synaptics-cpt/tourmalet/Docs/Pictures/Full_size/5223_battery_contact.jpg

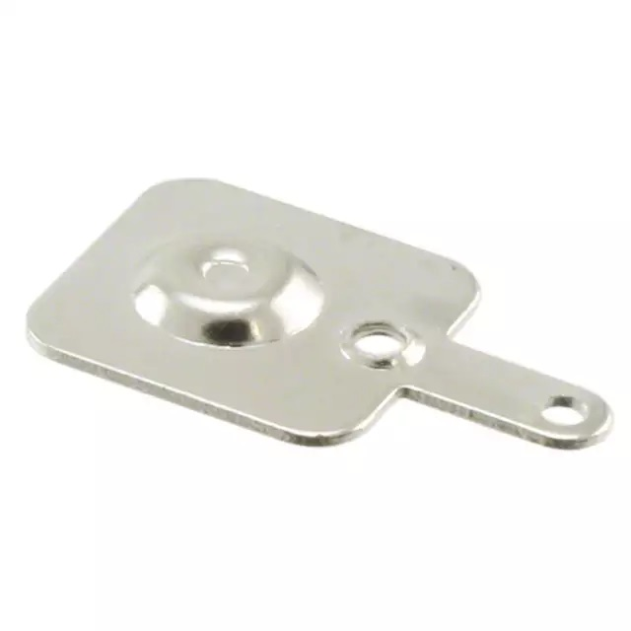
Docs/Pictures/Full_size/5223_battery_contact.jpg
