synaptics-cpt/tourmalet/Docs/Pictures/Full_size/attached_halves.jpg

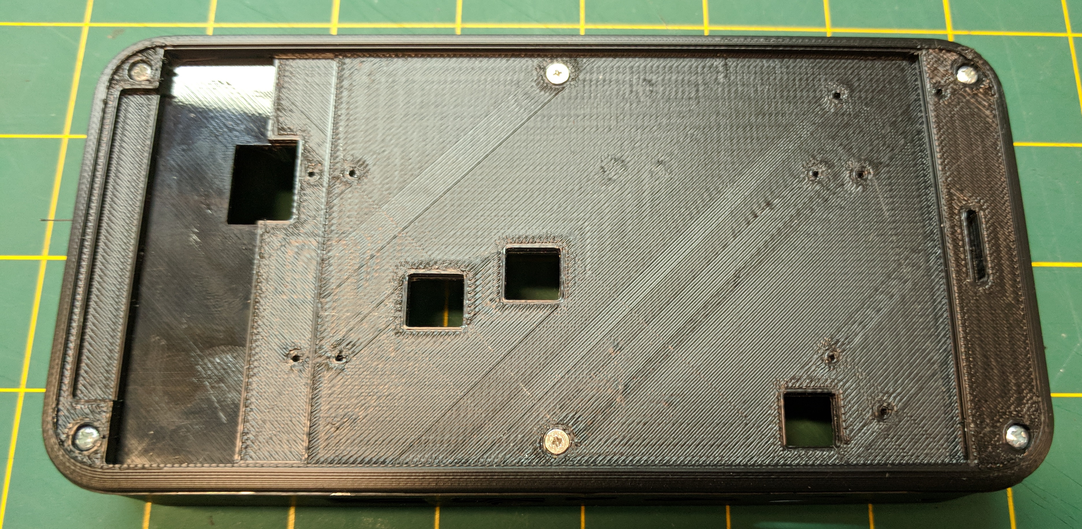
Docs/Pictures/Full_size/attached_halves.jpg
