synaptics-cpt/tourmalet/Docs/Pictures/Full_size/Back_no_battery.jpg

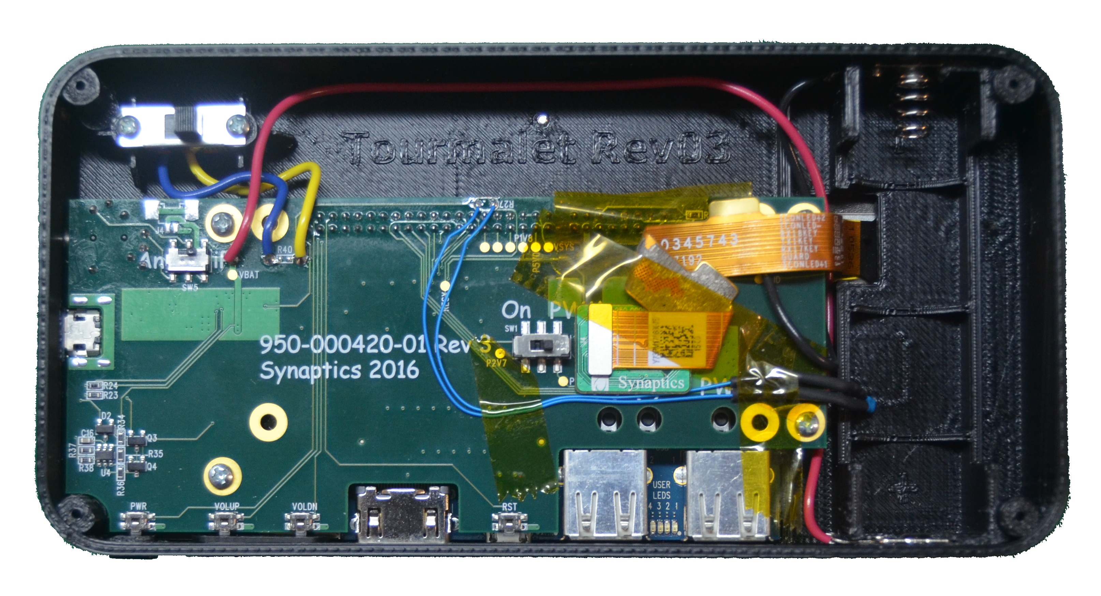
Docs/Pictures/Full_size/Back_no_battery.jpg
