synaptics-cpt/tourmalet/Docs/Pictures/Full_size/buttons.jpg

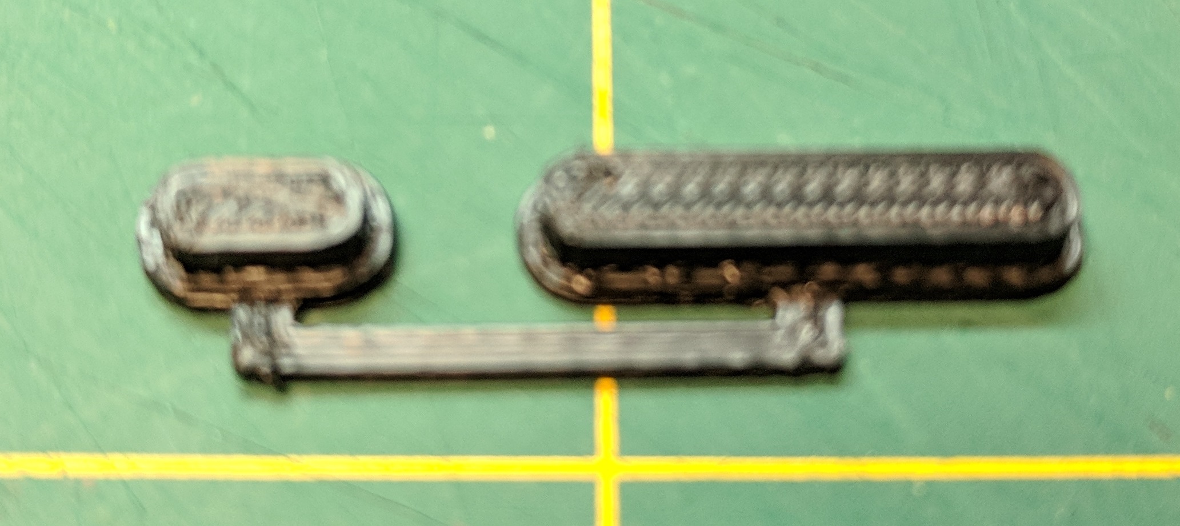
Docs/Pictures/Full_size/buttons.jpg
