synaptics-cpt/tourmalet/Docs/Pictures/Full_size/buttons_in.jpg

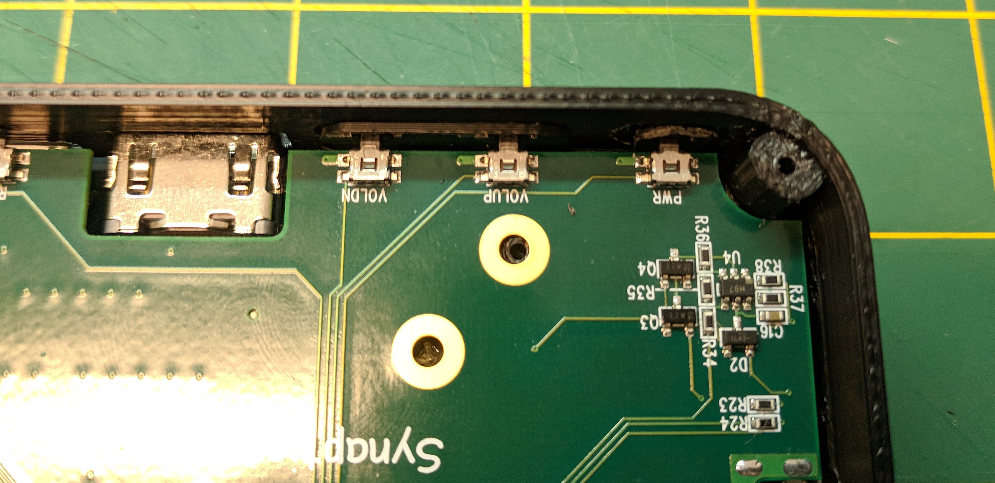
Docs/Pictures/Full_size/buttons_in.jpg
