synaptics-cpt/tourmalet/Docs/Pictures/Full_size/case_bottom.jpg

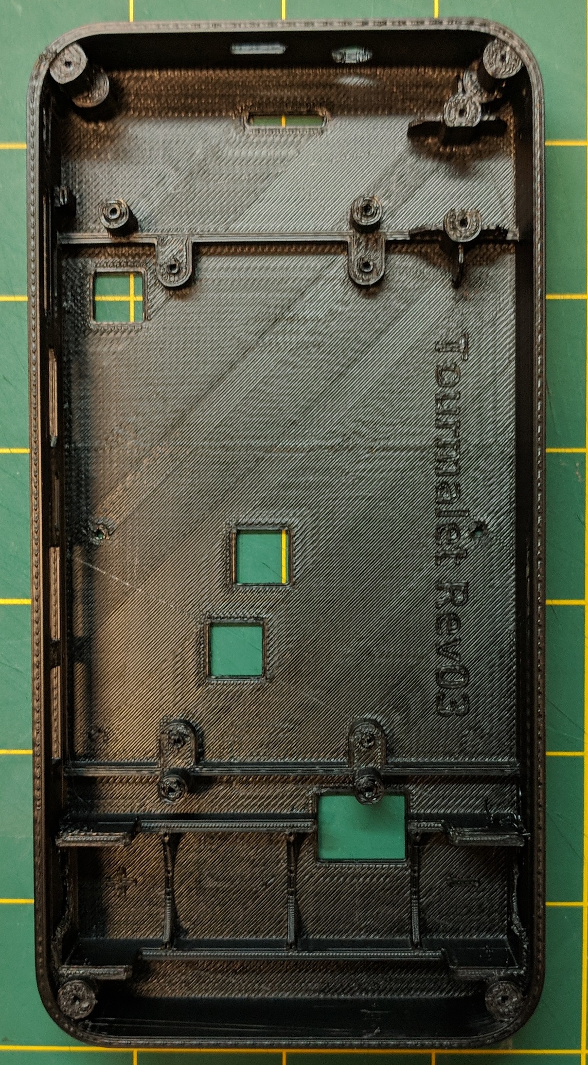
Docs/Pictures/Full_size/case_bottom.jpg
