synaptics-cpt/tourmalet/Docs/Pictures/Full_size/case_halves.jpg

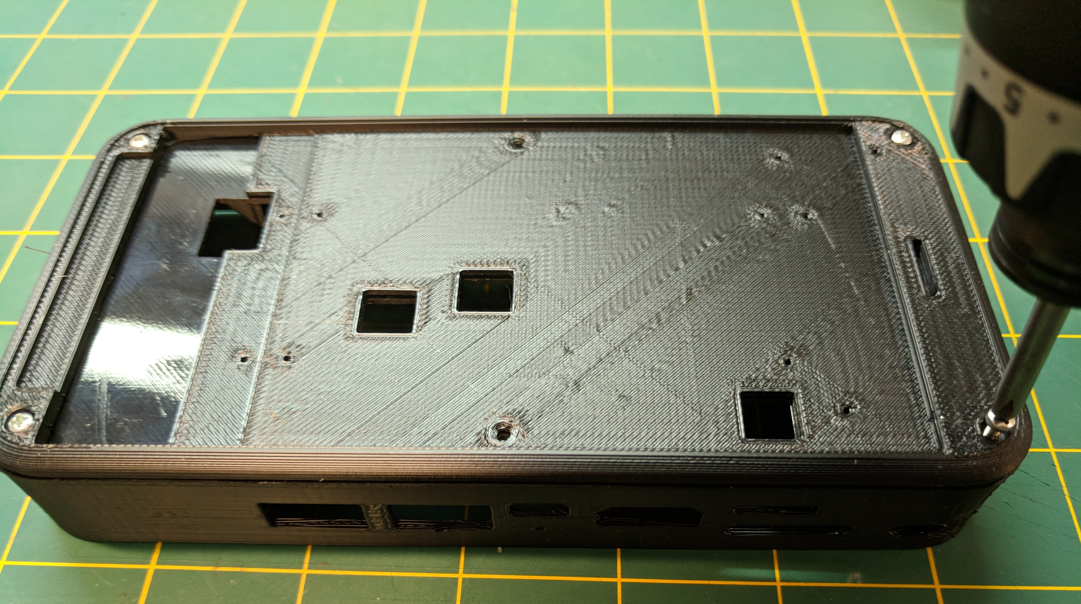
Docs/Pictures/Full_size/case_halves.jpg
