synaptics-cpt/tourmalet/Docs/Pictures/Full_size/case_top.jpg

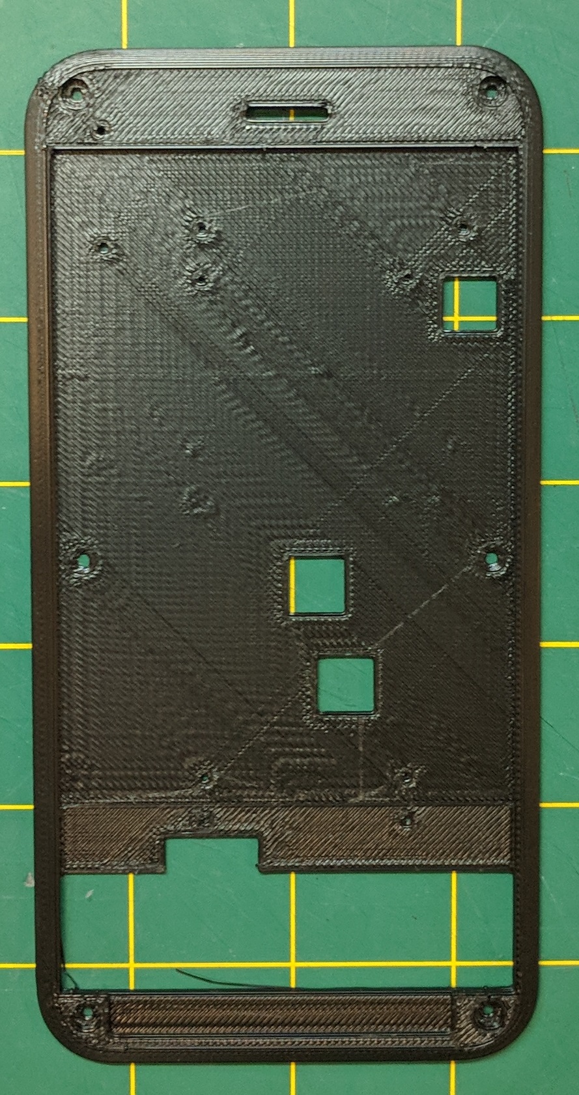
Docs/Pictures/Full_size/case_top.jpg
