synaptics-cpt/tourmalet/Docs/Pictures/Full_size/daughter_board_in.jpg

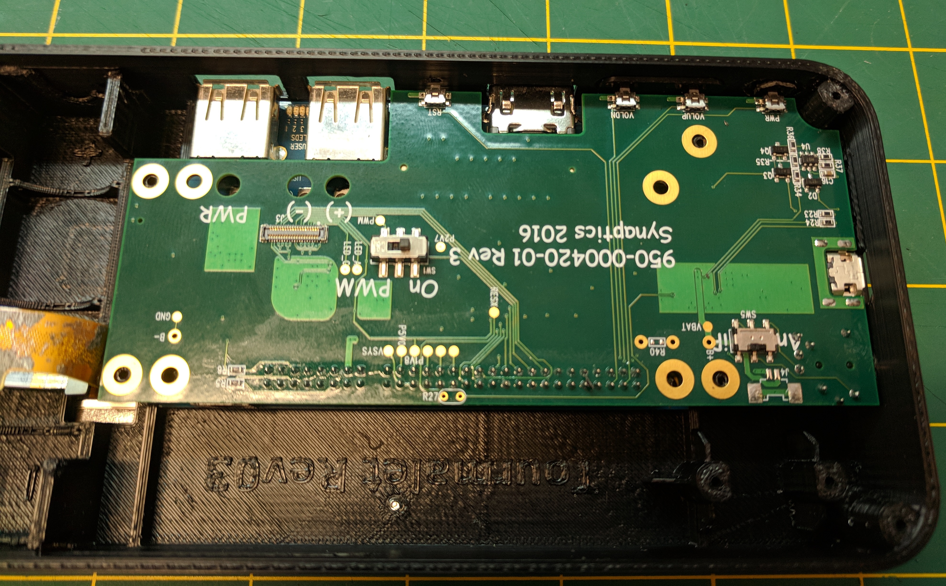
Docs/Pictures/Full_size/daughter_board_in.jpg
