synaptics-cpt/tourmalet/Docs/Pictures/Full_size/dragonboard_in_housing.jpg

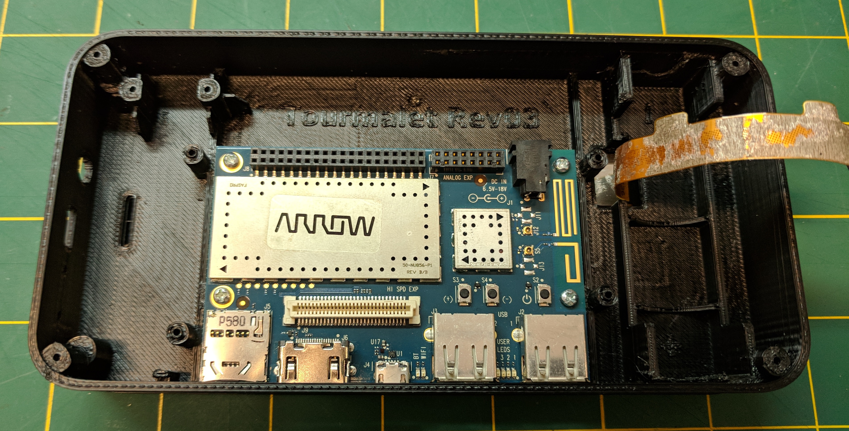
Docs/Pictures/Full_size/dragonboard_in_housing.jpg
