synaptics-cpt/tourmalet/Docs/Pictures/Full_size/fastboot_enable.jpg

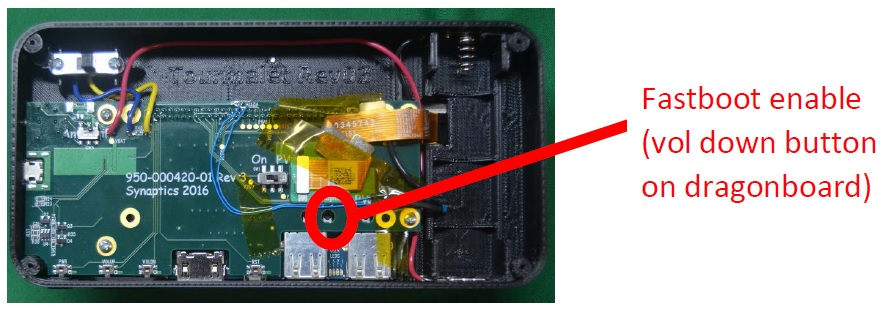
Docs/Pictures/Full_size/fastboot_enable.jpg
