synaptics-cpt/tourmalet/Docs/Pictures/Full_size/Glamor_shot_v1device.jpg

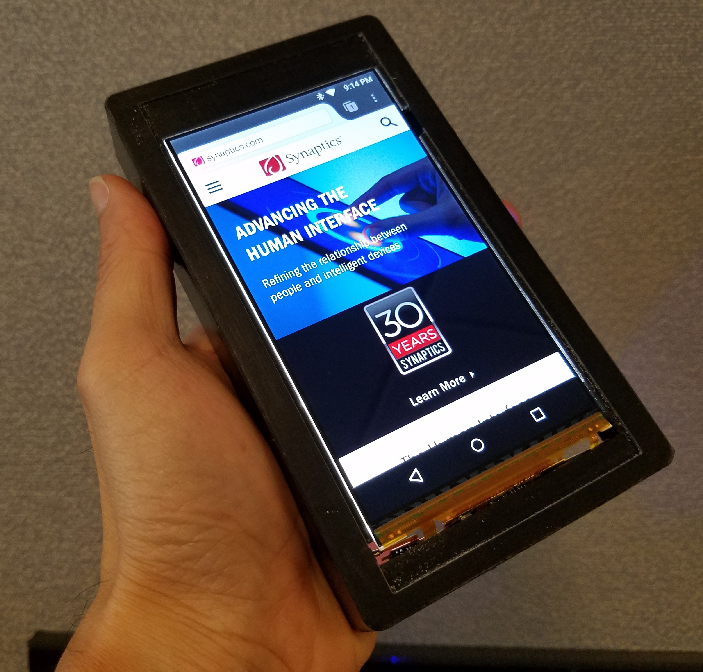
Docs/Pictures/Full_size/Glamor_shot_v1device.jpg
