synaptics-cpt/tourmalet/Docs/Pictures/Full_size/Headphone_switch.jpg

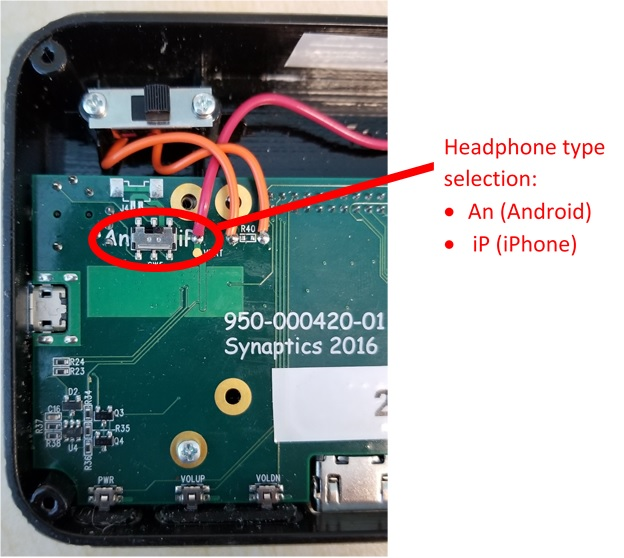
Docs/Pictures/Full_size/Headphone_switch.jpg
