synaptics-cpt/tourmalet/Docs/Pictures/Full_size/Home_screen.jpg

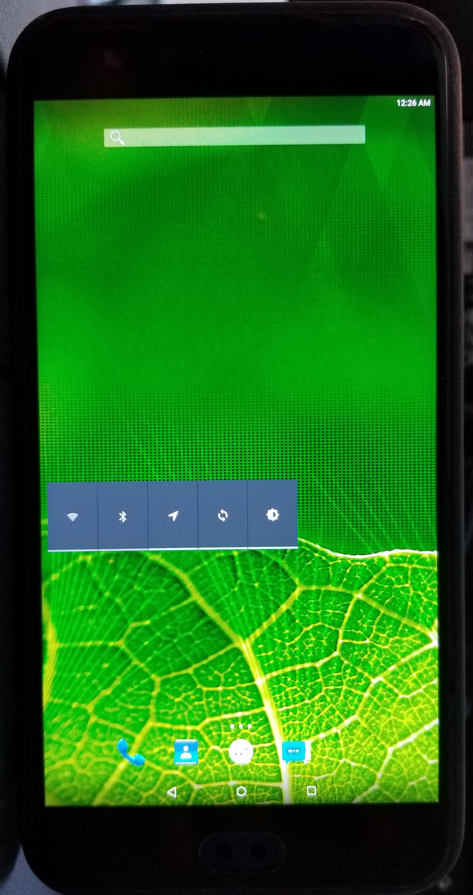
Docs/Pictures/Full_size/Home_screen.jpg
