synaptics-cpt/tourmalet/Docs/Pictures/Full_size/lcd_adapter.jpg

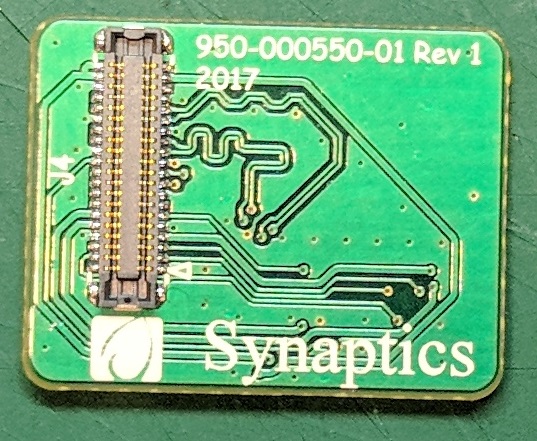
Docs/Pictures/Full_size/lcd_adapter.jpg
