synaptics-cpt/tourmalet/Docs/Pictures/Full_size/Lock_screen.jpg

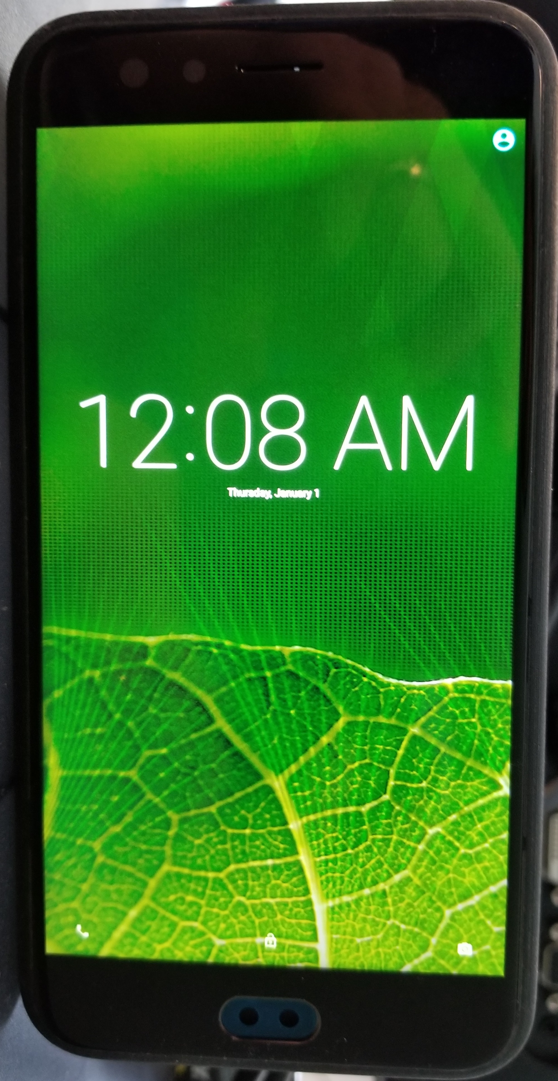
Docs/Pictures/Full_size/Lock_screen.jpg
