synaptics-cpt/tourmalet/Docs/Pictures/Full_size/negative_wire.jpg

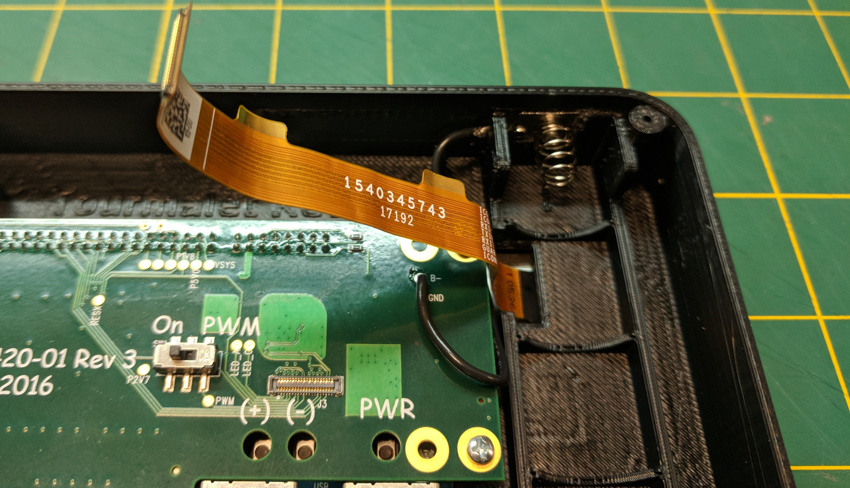
Docs/Pictures/Full_size/negative_wire.jpg
