synaptics-cpt/tourmalet/Docs/Pictures/Full_size/screen_adhesive_bottom.jpg

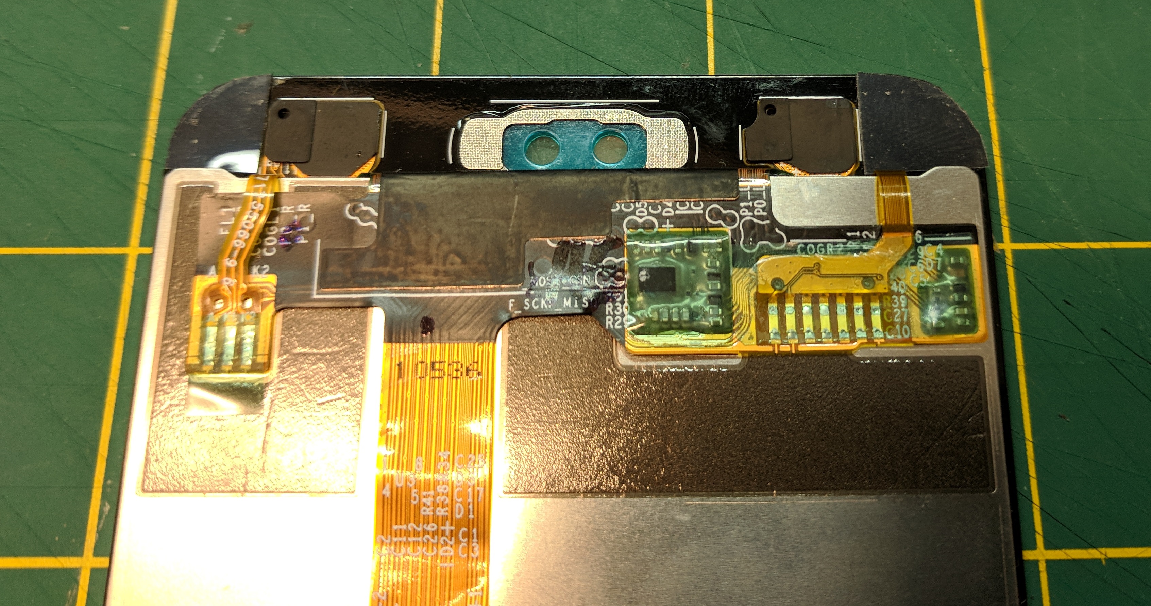
Docs/Pictures/Full_size/screen_adhesive_bottom.jpg
