synaptics-cpt/tourmalet/Docs/Pictures/Full_size/screen_adhesive_top.jpg

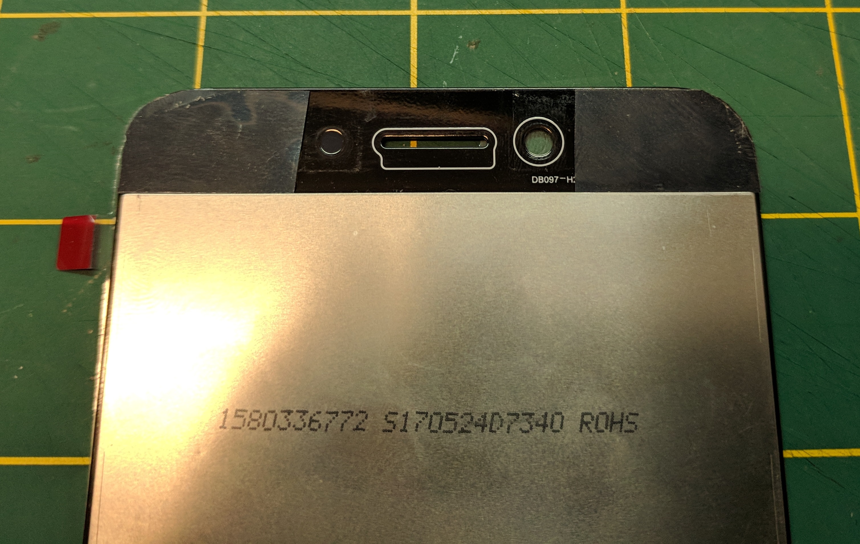
Docs/Pictures/Full_size/screen_adhesive_top.jpg
