synaptics-cpt/tourmalet/Docs/Pictures/Full_size/screen_on_housing.jpg

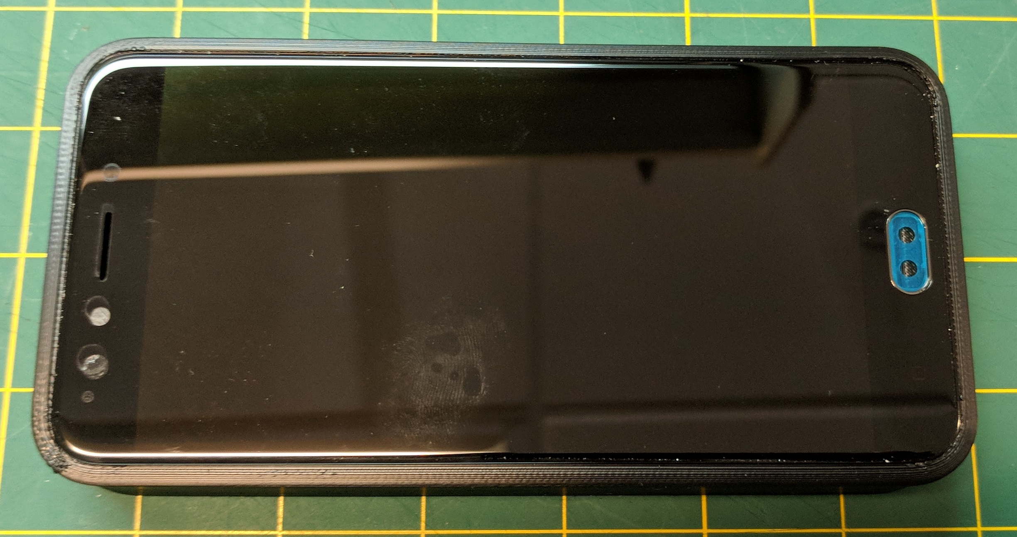
Docs/Pictures/Full_size/screen_on_housing.jpg
