synaptics-cpt/tourmalet/Docs/Pictures/Full_size/Touchscreen.jpg

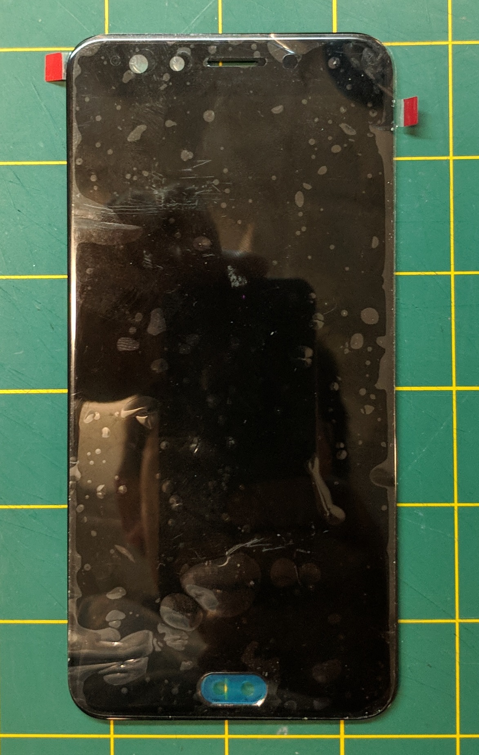
Docs/Pictures/Full_size/Touchscreen.jpg
