synaptics-cpt/tourmalet/Docs/Pictures/Full_size/touchscreen_back.jpg

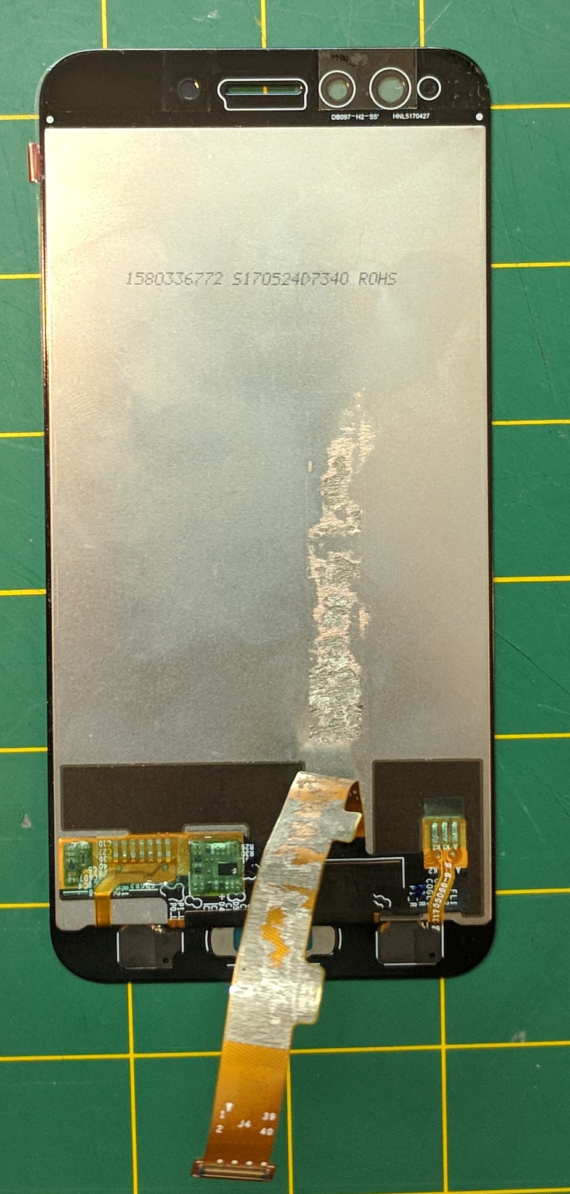
Docs/Pictures/Full_size/touchscreen_back.jpg
