synaptics-cpt/tourmalet/Docs/Pictures/Full_size/wired_contact.jpg

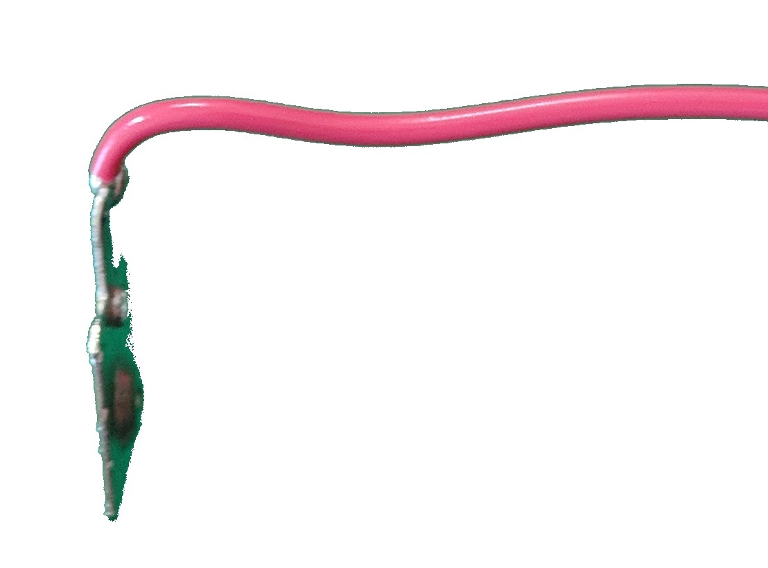
Docs/Pictures/Full_size/wired_contact.jpg
