synaptics-cpt/tourmalet/Docs/Pictures/Full_size/wired_switch.jpg

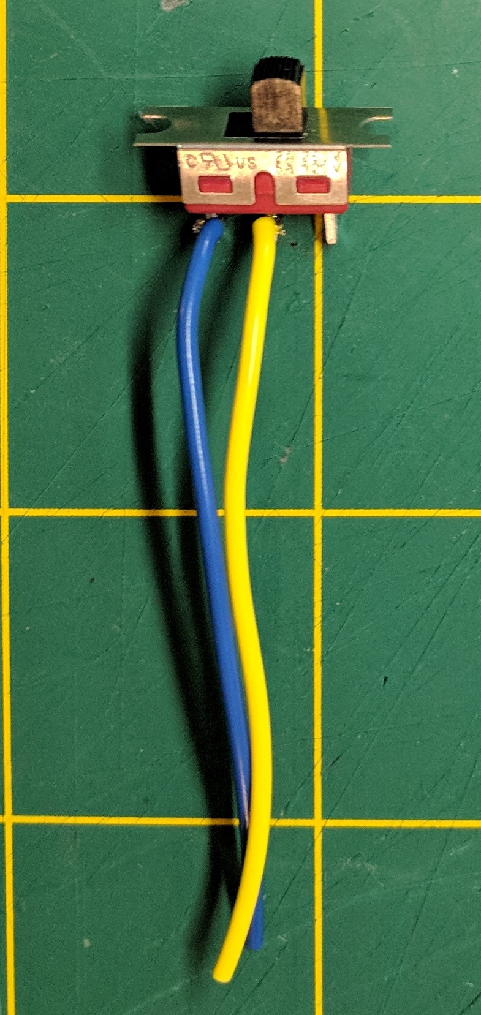
Docs/Pictures/Full_size/wired_switch.jpg
