synaptics-cpt/tourmalet/Docs/Pictures/Small/positive_wire.jpg

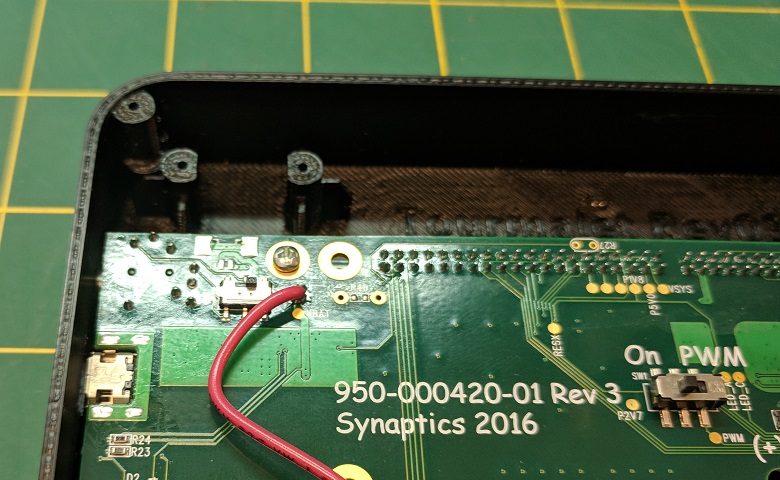
Docs/Pictures/Small/positive_wire.jpg
